KnightHill/daisy-pod-expander/oled_exp/spi/oled_exp.h

#pragma once
#ifndef OLED_EXP_H
#define OLED_EXP_H

#include "daisy_seed.h"

namespace daisy
{
/**
    @brief Class that handles initializing all of the hardware specific to the Daisy Patch Board. \n
    Helper funtions are also in place to provide easy access to built-in controls and peripherals.
    @author Stephen Hensley
    @date November 2019
    @ingroup boards
*/

using MyOledDisplay = OledDisplay<SSD130x4WireSpi128x64Driver>;

class OledExp
{
public:
  /** Switches */
  enum Sw {
    BUTTON_1,    /** & */
    BUTTON_2,    /** & */
    BUTTON_3,    /** & */
    BUTTON_LAST, /** & */
  };

  /** Knobs */
  enum Knob {
    KNOB_1,    /** &  */
    KNOB_2,    /** & */
    KNOB_3,    /** &  */
    KNOB_4,    /** & */
    KNOB_LAST, /** & */
  };

  OledExp() {}
  ~OledExp() {}

  /** Init related stuff. */
  void Init(bool boost = false);

  /** Wait for a bit
  \param del Time to wait in ms.
  */
  void DelayMs(size_t del);

  /** Starts the callback
  \param cb Interleaved callback function
  */
  void StartAudio(AudioHandle::InterleavingAudioCallback cb);

  /** Starts the callback
  \param cb multichannel callback function
  */
  void StartAudio(AudioHandle::AudioCallback cb);

  /**
     Switch callback functions
     \param cb New interleaved callback function.
  */
  void ChangeAudioCallback(AudioHandle::InterleavingAudioCallback cb);

  /**
     Switch callback functions
     \param cb New multichannel callback function.
  */
  void ChangeAudioCallback(AudioHandle::AudioCallback cb);

  /** Stops the audio if it is running. */
  void StopAudio();

  /** Updates the Audio Sample Rate, and reinitializes.
   ** Audio must be stopped for this to work.
   */
  void SetAudioSampleRate(SaiHandle::Config::SampleRate samplerate);

  /** Returns the audio sample rate in Hz as a floating point number.
   */
  float AudioSampleRate();

  /** Sets the number of samples processed per channel by the audio callback.
   */
  void SetAudioBlockSize(size_t blocksize);

  /** Returns the number of samples per channel in a block of audio. */
  size_t AudioBlockSize();

  /** Returns the rate in Hz that the Audio callback is called */
  float AudioCallbackRate();

  /**
     Start analog to digital conversion.
   */
  void StartAdc();

  /** Stops Transfering data from the ADC */
  void StopAdc();

  /** Call at same rate as analog reads for smooth reading.*/
  void ProcessAnalogControls();

  /** Process Analog and Digital Controls */
  inline void ProcessAllControls()
  {
    ProcessAnalogControls();
    ProcessDigitalControls();
  }

  /** & */
  float GetKnobValue(Knob k);

  /** Process digital controls */
  void ProcessDigitalControls();

  /** Reset Leds*/
  void ClearLeds();

  /** Update Leds to set colors*/
  void UpdateLeds();

  /** Public Members */
  DaisySeed seed;            /**<# */
  Encoder encoder;           /**< & */
  AnalogControl knob1,       /**< & */
      knob2,                 /**< & */
      knob3,                 /**< & */
      knob4,                 /**< & */
      *knobs[KNOB_LAST];     /**< & */
  Switch button1,            /**< & */
      button2,               /**< & */
      button3,               /**< & */
      *buttons[BUTTON_LAST]; /**< & */
  RgbLed led1,               /**< & */
      led2;                  /**< & */
  MidiUartHandler midi;
  MyOledDisplay display;

private:
  void SetHidUpdateRates();
  void InitButtons();
  void InitEncoder();
  void InitLeds();
  void InitKnobs();
  void InitMidi();
  void InitDisplay();
};

} // namespace daisy
#endif
